Person-0/PicoDAC/assets/board2_rough.webp

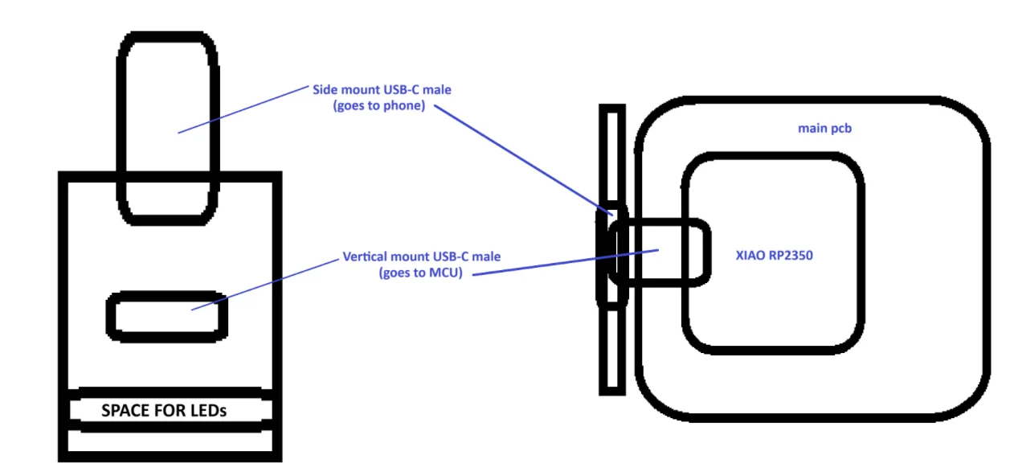
assets/board2_rough.webp
