Person-0/PicoDAC/assets/board_roughsketch_2.webp

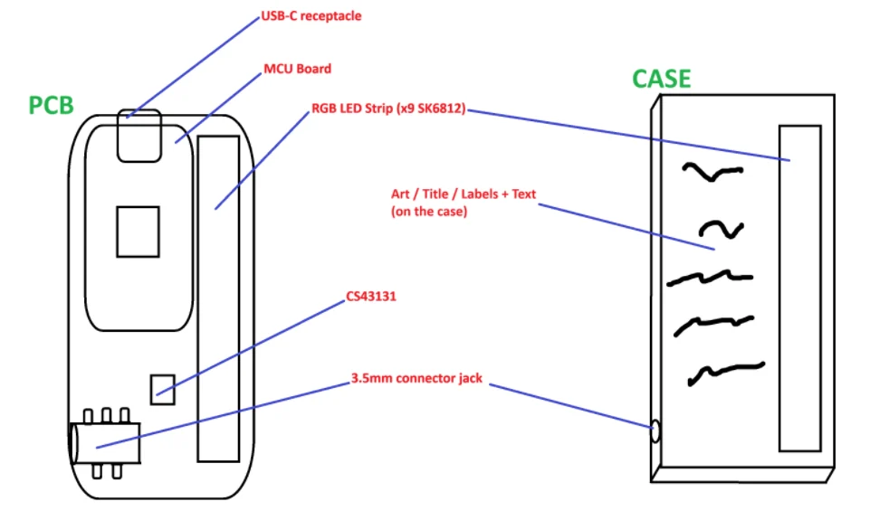
assets/board_roughsketch_2.webp
