Person-0/PicoDAC/assets/pcb_preview.webp

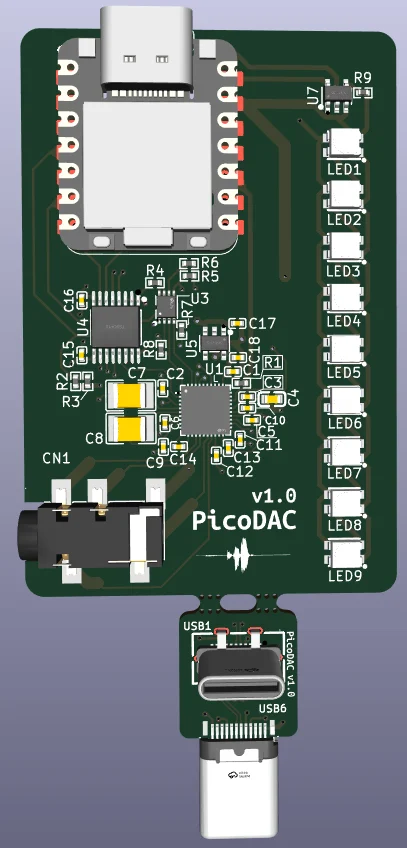
assets/pcb_preview.webp
