Person-0/PicoDAC/assets/pcb_r1_b1.png

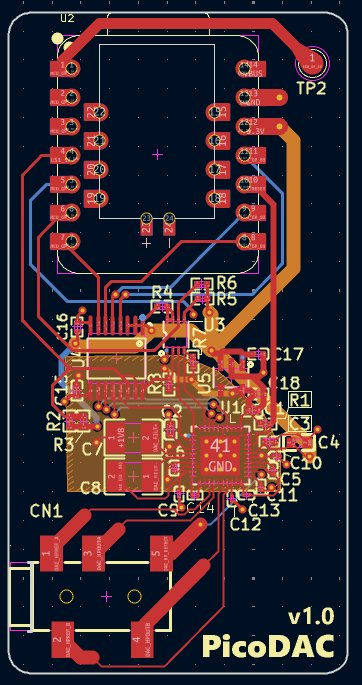
assets/pcb_r1_b1.png
