Person-0/PicoDAC/assets/pcb_r1_b2.png

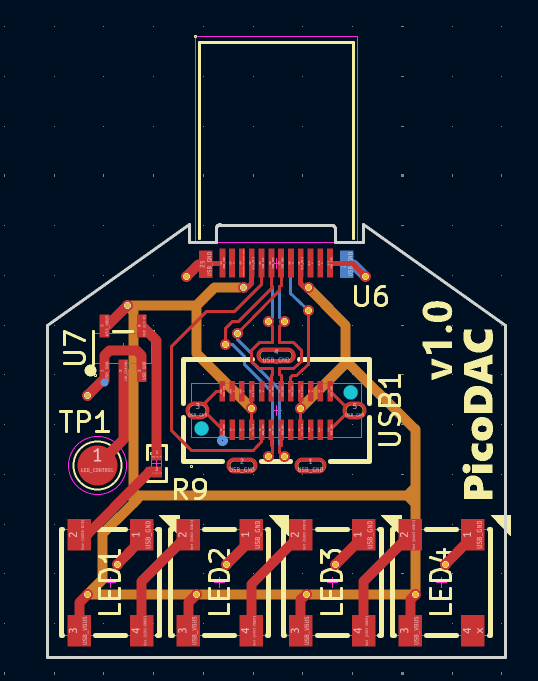
assets/pcb_r1_b2.png
