Person-0/PicoDAC/assets/pcb_r2_b1.png

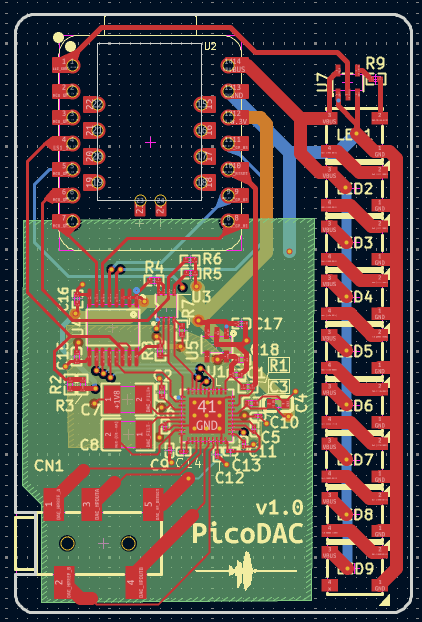
assets/pcb_r2_b1.png
