Person-0/PicoDAC/assets/pcb_r2_b2.png

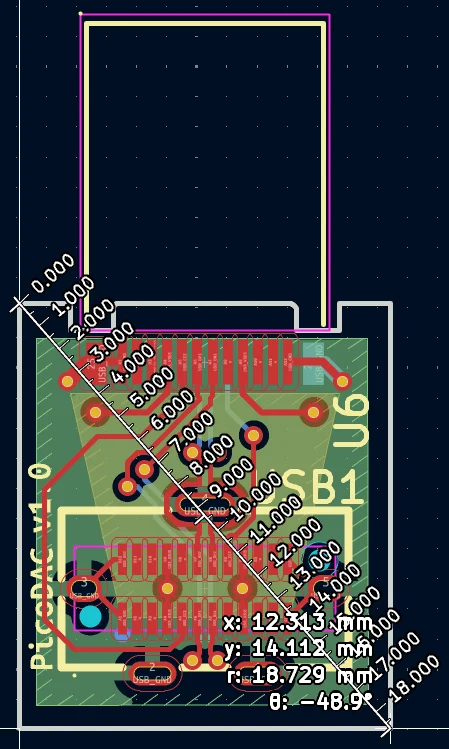
assets/pcb_r2_b2.png
