Person-0/PicoDAC/assets/pcb_r3_b1.png

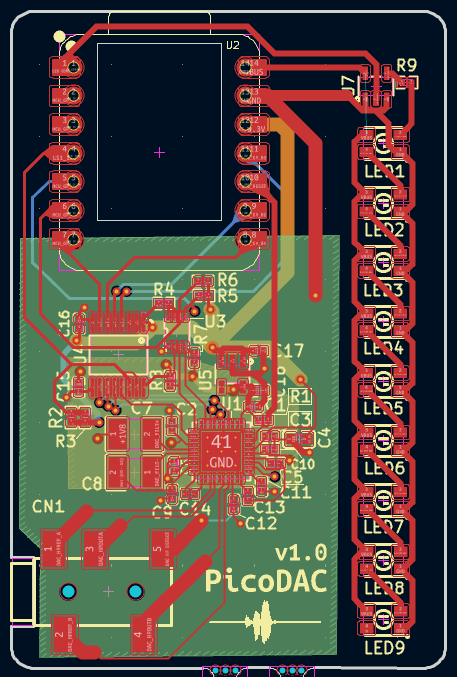
assets/pcb_r3_b1.png
