Person-0/PicoDAC/assets/pcb_r3_b2.png

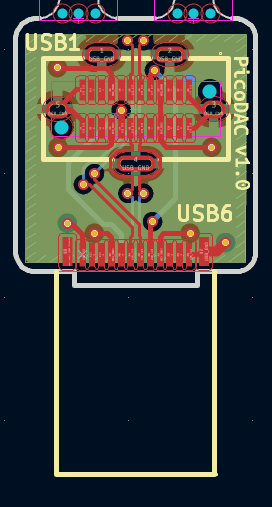
assets/pcb_r3_b2.png
