Person-0/PicoDAC/assets/pcb_r4_b1.png

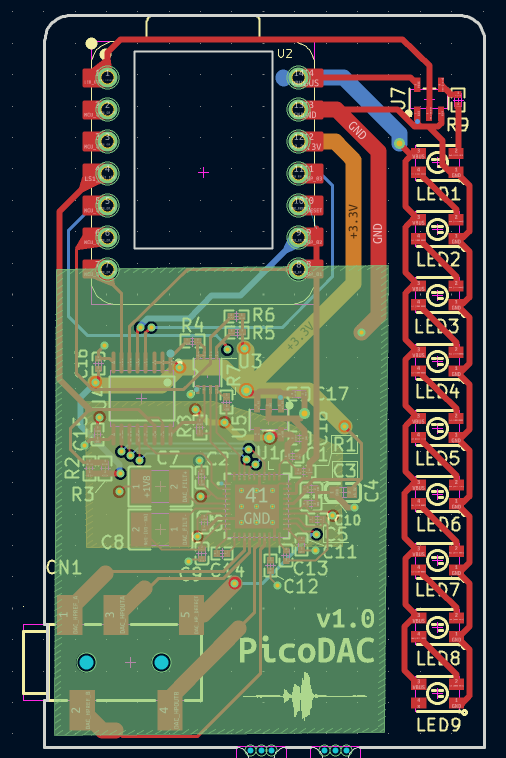
assets/pcb_r4_b1.png
