Person-0/PicoDAC/assets/pcb_r4_b2.png

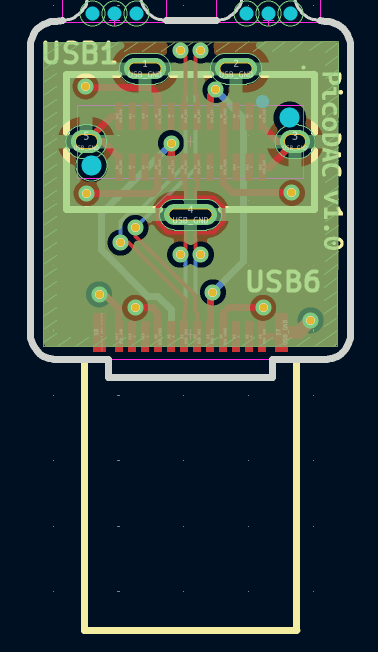
assets/pcb_r4_b2.png
